jackrmcshane/embedded_systems/sidepiece/bdc.py

"""
Author(s): Rob Hageboeck & Jack McShane
Date: March 28, 2022
Filename: bdc.py

'bdc.py' or 'Bridge Data Collector' draws on the Python3 adxl343 module
to sample and store acceleration data from the bridge to be assembled
into a database for machine learning projects involving bridge usage,
gait analysis, and low/high pass filtering.
"""

import spidev
import time

def log(ts,x,y,z):
	pass

def sample():
	pass

if __name__ == "__main__":
	print("")
