jackrmcshane/embedded_systems/lab6/stm32/Core/Src/menu.c

#include "main.h"

extern uint8_t timer_done;
extern uint32_t period;
extern RTC_HandleTypeDef hrtc;
extern ADC_HandleTypeDef hadc1;
extern TIM_HandleTypeDef htim2;
extern flash_status_t fs;

typedef struct command {
  char * cmd_string;
  void (*cmd_function)(char * arg);
} command_t;

command_t commands[] = {
  {"help",help_command},
  {"lof",lof_command},
  {"lon",lon_command},
  {"test",test_command},
  {"ts",ts_command},
  {"ds",ds_command},
  {"tsl237",tsl237_command},
  {"temp",temp_command},
  {"battery",battery_command},
  {"sample",sample_command},
  {"ef",erase_flash_command},
  {"log", log_command},
  {"data", data_command},
  {0,0}
};


/*
 * need to fix printing of the timestamp once we figure out the format for it
 */
void log_command(char *arguments){

  uint8_t month = 0, day = 0, year = 0, hours = 0, minutes = 0, seconds = 0;

  uint64_t * addr = fs.data_start;
  logdata_t *ld = (logdata_t *)addr;
  char message[8];

  while(( addr >= fs.data_end ) && ( ld->watermark == 1)){
    
    if( ld->status == 2 ){ // if is log data
      unpack(ld->timestamp,&month,&day,&year,&hours,&minutes,&seconds);

      printf("L,%d,%d/%d/%d,%d:%d:%d,", ld->status, month,day,year, hours,minutes,seconds);
      for(uint i = 0; i < 8; i++)
        printf("%c", ld->msg[i]);

      printf("\n\r");
    }

    addr -= 2;
    ld = (logdata_t *)addr;
  }

  printf("OK\n\r");
}


// echo sensor data
void data_command(char *arguments){
  uint8_t month, day, year, hours, minutes, seconds;

  uint64_t * memptr = fs.data_start;
  sensordata_t * sd = (sensordata_t *)fs.data_start;

  while(sd >= fs.data_end && sd->watermark == 1){
    if(sd->status == 1){
      unpack(sd->timestamp,&month,&day,&year,&hours,&minutes,&seconds);
      printf("D,%d,%d/%d/%d,%d:%d:%d,%d.%d,%d,%.3f\n\r",
             sd->status,
             month,day,year,
             hours,minutes,seconds,
             sd->battery_voltage / 1000,
             sd->battery_voltage % 1000,
             sd->temperature,
             ((float)sd->sensor_period) / 1000);
    }

    memptr -= 2;
    sd = (sensordata_t *)memptr;
  }

  printf("OK\n\r");
}


void sample_command(char *arguments){
  sample();
}


void erase_flash_command(char* args){
  
  if( !args ){
    printf("NOK\n\r");
    return;

  } else {

    if( !strcmp("all", args) ){
      flash_erase();
      printf("Erased all flash!\n\r");

    } else {
      printf("NOK\n\r");
    }

  }

  printf("OK\n\r");
}


void help_command(char *arguments) {

  uint16_t ncommands = (sizeof(commands) / sizeof(commands[0])) - 1;
  printf("Available Commands:\n\r");
  for( int i = 0; i < ncommands; i++ )
    printf("%s\n\r", commands[i].cmd_string);

  printf("OK\r\n");
}

void lof_command(char *arguments) {
  HAL_GPIO_WritePin(LD3_GPIO_Port, LD3_Pin, GPIO_PIN_RESET);
  printf("OK\r\n");
}
void lon_command(char *arguments) {
  HAL_GPIO_WritePin(LD3_GPIO_Port, LD3_Pin, GPIO_PIN_SET);
  printf("OK\r\n");
}
void test_command(char *arguments) {
}
void ts_command(char *arguments){
  RTC_TimeTypeDef current_time;
  char *arg;
  int arg_count = 0;
  if (arguments == NULL) {
    printf("NOK\r\n");
    return;
  }
  arg = strtok(arguments,",");
  while (arg != NULL) {
    switch (arg_count) {
      case 0:
        current_time.Hours = (int) strtol(arg,NULL,10);
        if (current_time.Hours > 24 || current_time.Hours < 0) {
          printf("NOK\r\n");
          return;
        }
        break;
      case 1:
        current_time.Minutes = (int) strtol(arg,NULL,10);
        if (current_time.Minutes > 59 || current_time.Minutes < 0) {
          printf("NOK\r\n");
          return;
        }
        break;
      case 2:
        current_time.Seconds = (int) strtol(arg,NULL,10);
        if (current_time.Seconds > 59 || current_time.Seconds < 0) {
          printf("NOK\r\n");
          return;
        }
        break;
      default:
        printf("NOK\r\n");
        return;
        break;
    }
    arg = strtok(NULL,",");
    arg_count++;
  }
  if (arg_count < 3) {
    printf("NOK\r\n");
    return;
  }
  HAL_RTC_SetTime(&hrtc,&current_time,RTC_FORMAT_BIN);
  printf("OK\r\n");
}
void ds_command(char *arguments) {
  RTC_DateTypeDef current_date;
  char *arg;
  int arg_count = 0;
  if (arguments == NULL) {
    printf("NOK\r\n");
    return;
  }
  arg = strtok(arguments,",");
  while (arg != NULL) {
    switch (arg_count) {
      case 0:
        current_date.Month = (int) strtol(arg,NULL,10);
        if (current_date.Month > 12 || current_date.Month < 0) {
          printf("NOK\r\n");
          return;
        }
        break;
      case 1:
        current_date.Date = (int) strtol(arg,NULL,10);
        if (current_date.Date > 31 || current_date.Date < 0) {
          printf("NOK\r\n");
          return;
        }
        break;
      case 2:
        current_date.Year = (int) strtol(arg,NULL,10);
        if (current_date.Year < 0 || current_date.Year > 99) {
          printf("NOK\r\n");
          return;
        }
        break;
      default:
        printf("NOK\r\n");
        return;
        break;
    }
    arg = strtok(NULL,",");
    arg_count++;
  }
  if (arg_count < 3) {
    printf("NOK\r\n");
    return;
  }
  HAL_RTC_SetDate(&hrtc,&current_date,RTC_FORMAT_BIN);
  printf("OK\r\n");
}

float read_light_sensor( void ) {

  float clock_period, sensor_period, sensor_frequency;

  timer_done = 0;
  HAL_TIM_IC_Start_IT(&htim2, TIM_CHANNEL_1); // enable timer interrupts
  while(!timer_done); // while callback not finished

  clock_period = SystemCoreClock;
  clock_period = 1/clock_period;
  sensor_period = clock_period * (float)period;
  sensor_frequency = 1/sensor_period;

  return sensor_frequency;
}

void tsl237_command(char *arguments) {

  if(arguments){
    printf("NOK\n\r");
  } else {
    printf("%0.3f hz\n\r", read_light_sensor());
    printf("OK\n\r");
  }
}

void temp_command(char *arguments) {

  if( arguments )
    printf("NOK\r\n");

  else {

    printf("%d C\n\r", ( int )read_temp());
    printf("OK\n\r");

  }
}

void battery_command(char *arguments) {

  uint32_t vbat;

  if( arguments ){

    printf("NOK\r\n");
    return;

  } else {

    vbat = read_vrefint();
    printf("%d.%03d V\n\r", ((int)vbat / 1000), ((int)vbat % 1000));
    printf("OK\n\r");

  }
}

void prompt() {
  RTC_TimeTypeDef current_time;
  RTC_DateTypeDef current_date;
  HAL_RTC_GetTime(&hrtc,&current_time,RTC_FORMAT_BIN);
  HAL_RTC_GetDate(&hrtc,&current_date,RTC_FORMAT_BIN);
  printf("%02d/%02d/%02d %02d:%02d:%02d IULS> ",current_date.Month,current_date.Date,current_date.Year,
                                        current_time.Hours,current_time.Minutes,current_time.Seconds);
}

int parse_command (uint8_t *line, uint8_t **command, uint8_t **args) {
  // Point command at the beginning of the buffer
  *command = line;
  for (;;line++) {
    if (*line == '\0') {
      *args = NULL;
      break;
    } else if (*line == ',') {
      *line = '\0';
      *args = (line+1);
      break;
    }
  }
  return 0;
}

int execute_command(uint8_t * line) {
  uint8_t *cmd;
  uint8_t *arg;
  command_t *p = commands;
  int success = 0;

  if (!line) {
    return (-1); // Passed a bad pointer 
  }
  if (parse_command(line,&cmd,&arg) == -1) {
    printf("Error with parse command\n\r");
    return (-1);
  }
  while (p->cmd_string) {
    if (!strcmp(p->cmd_string,(char *) cmd)) {
      if (!p->cmd_function) {
        return (-1);
      }
      (*p->cmd_function)((char *)arg); // Run the command with the passed arguments
      success = 1;
      break;
    }
    p++;
  }
  if (success) {
    return (0);
  }
  else {
    return (-1);
  }
}

void lon() {
  HAL_GPIO_WritePin(LD3_GPIO_Port, LD3_Pin, GPIO_PIN_SET);
}

void lof() {
  HAL_GPIO_WritePin(LD3_GPIO_Port, LD3_Pin, GPIO_PIN_RESET);
}

void unpack(
  uint32_t packedBits,
  uint8_t *month, uint8_t *day, uint8_t *year,
  uint8_t *hours, uint8_t *minutes, uint8_t *seconds) {
  // 32 bits for timestamp (uint32_t)
  // Date
  // Month:  1-12 // 4 bits
  // Date:   1-31 // 5 bits
  // Year:   0-63 // 6 bits - edge of amount
  // Time
  // Hour:   0-24 // 5 bits
  // Minute: 0-59 // 6 bits
  // Seconds:0-59 // 6 bits
  // Packing Order
  //MONTH|DAY|YEAR|HOURS|MINUTES|SECONDS
  *seconds = packedBits & 0b111111;
  packedBits >>= 6;
  *minutes = packedBits & 0b111111;
  packedBits >>= 6;
  *hours = packedBits &   0b11111;
  packedBits >>= 5;
  *year = packedBits &    0b111111;
  packedBits >>= 6;
  *day = packedBits &     0b11111;
  packedBits >>= 5;
  *month = packedBits &   0b1111;
}

uint32_t pack(uint8_t month, uint8_t day, uint8_t year,
  uint8_t hours, uint8_t minutes, uint8_t seconds) {
    uint32_t packedBits = 0;
    packedBits |= (month &   0b1111);
    packedBits <<= 5;
    packedBits |= (day &     0b11111);
    packedBits <<= 6;
    packedBits |= (year &    0b111111);
    packedBits <<= 5;
    packedBits |= (hours &   0b11111);
    packedBits <<= 6;
    packedBits |= (minutes & 0b111111);
    packedBits <<= 6;
    packedBits |= (seconds & 0b111111);
    return packedBits;
}
