jackrmcshane/embedded_systems/embsys_sp22/example/l432_flash/Core/Inc/led.h

/* led.h
 * Description: 
 *
 * Author: Bryce Himebaugh 
 * Contact: bhimebau@indiana.edu
 * Date: 02.25.2021
 * Copyright (C) 2021
 *
 */

void lon(void);
void lof(void);
void lon_command(char *arguments);
void lof_command(char *arguments);
