jackrmcshane/embedded_systems/embsys_sp22/example/l432_flash/Core/Inc/sample.h

/* sample.h
 * Description: 
 *
 * Author: Bryce Himebaugh 
 * Contact: bhimebau@indiana.edu
 * Date: 03.19.2021
 * Copyright (C) 2021
 *
 */

int sample(void);
int read_data_records(flash_status_t *);
